abdo20050/BlackFingersTeam/models/3D Robot case.jpeg

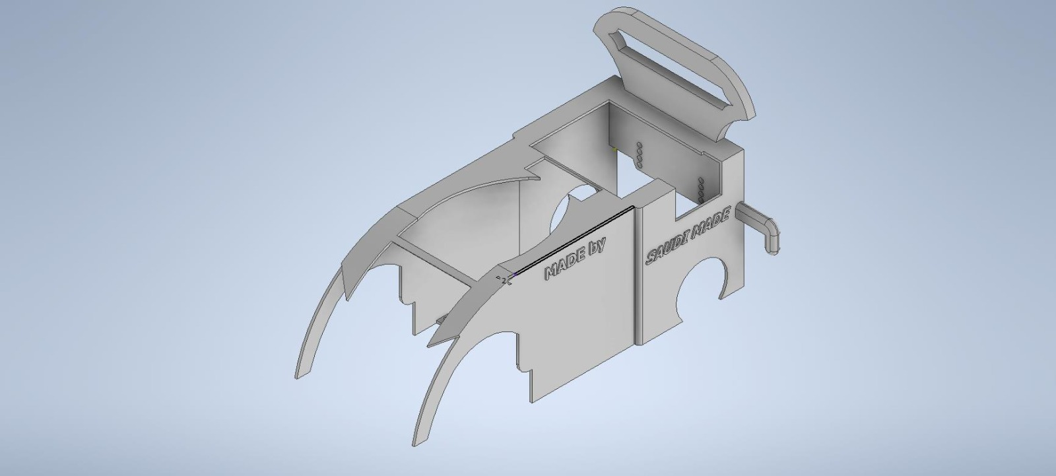
models/3D Robot case.jpeg
