abdo20050/BlackFingersTeam/models/3D vehicle structure main part.jpeg

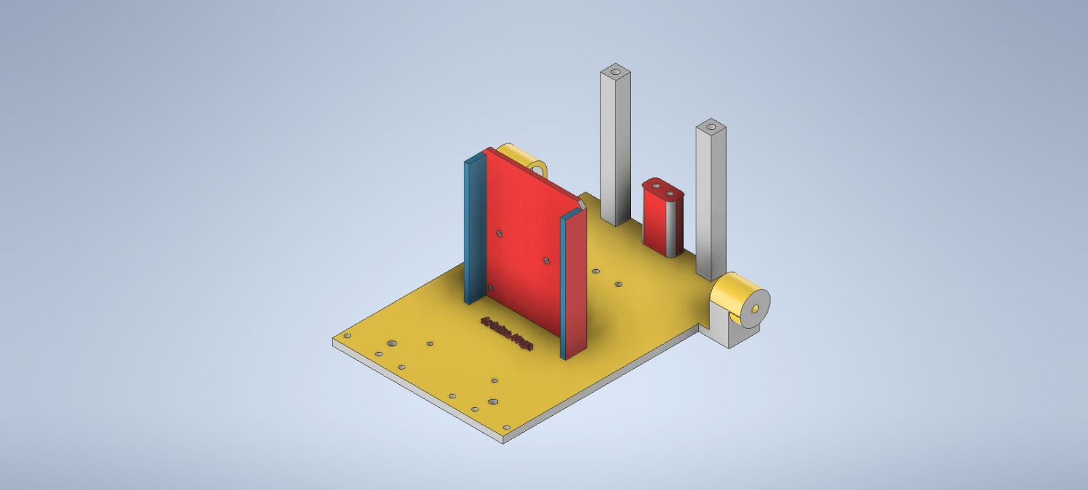
models/3D vehicle structure main part.jpeg
