abdo20050/BlackFingersTeam/models/acrylic pieces for wheels.jpg

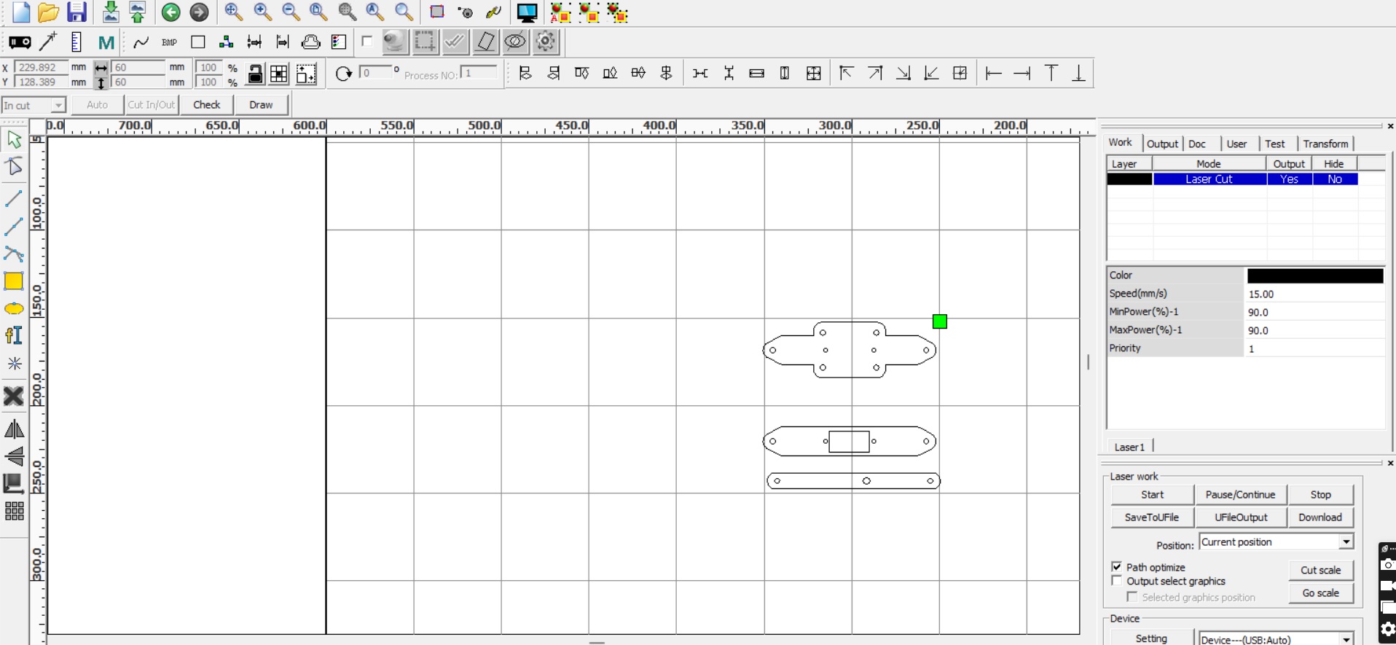
models/acrylic pieces for wheels.jpg
