abdo20050/BlackFingersTeam/models/ULTRASONIC BOX..jpg

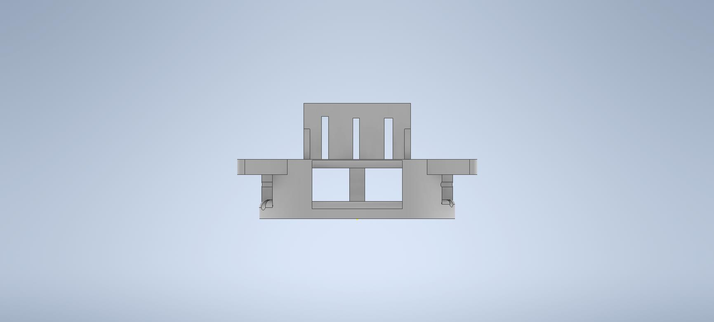
models/ULTRASONIC BOX..jpg
