abdo20050/BlackFingersTeam/schemes/circuit digram v2.jpeg

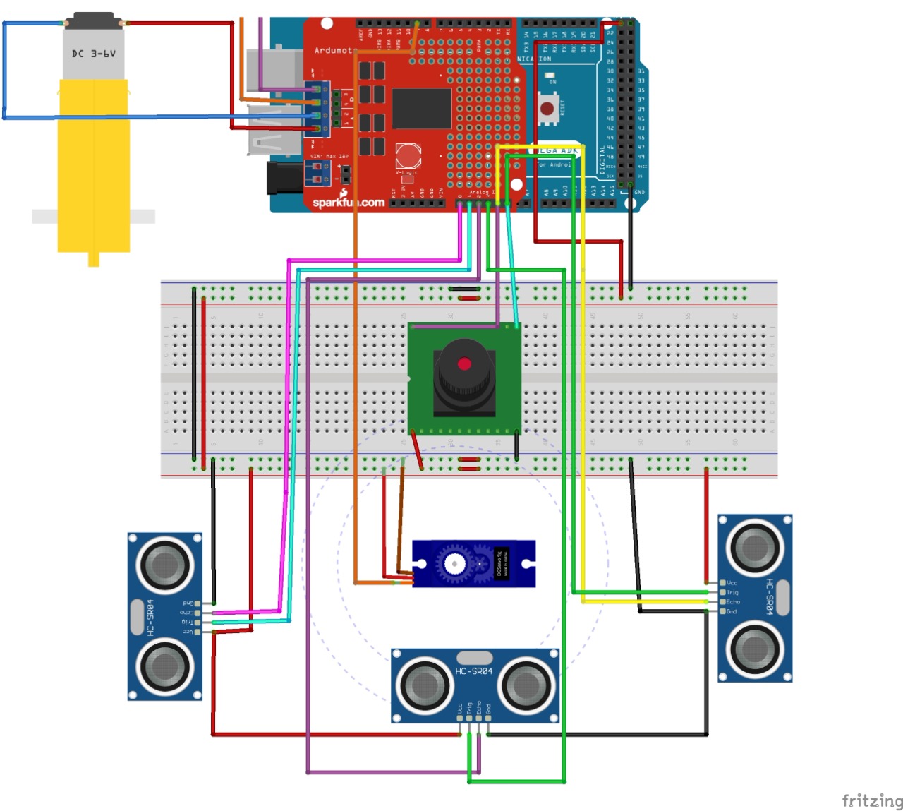
schemes/circuit digram v2.jpeg
