abdo20050/BlackFingersTeam/t - photos/FUNNY PHOTO.jpeg

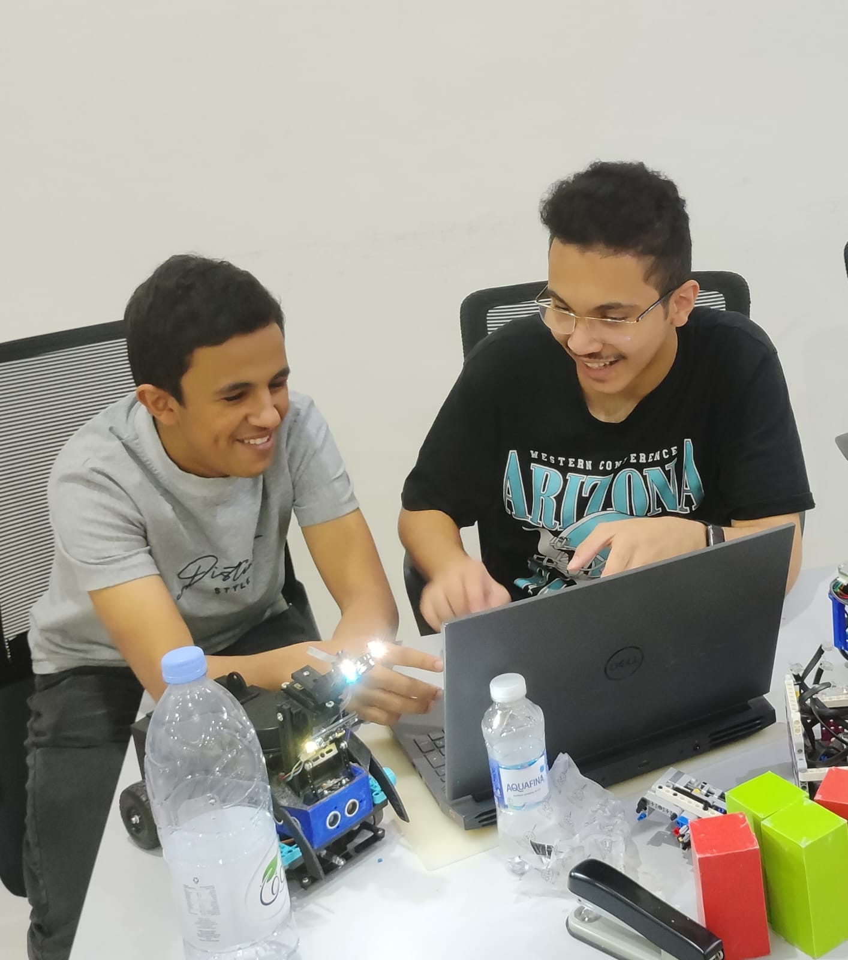
t - photos/FUNNY PHOTO.jpeg
