abdo20050/BlackFingersTeam/v- photos/DOWN SIDE.jpeg

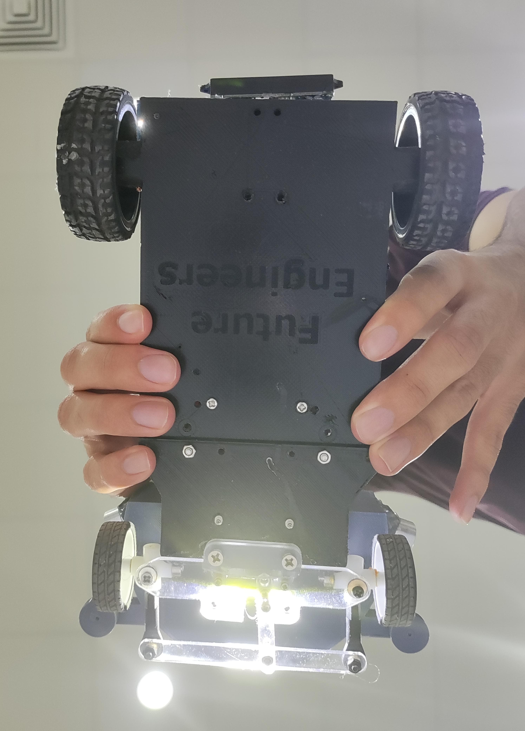
v- photos/DOWN SIDE.jpeg
