abdo20050/BlackFingersTeam/v- photos/FRONT SIDE.jpeg

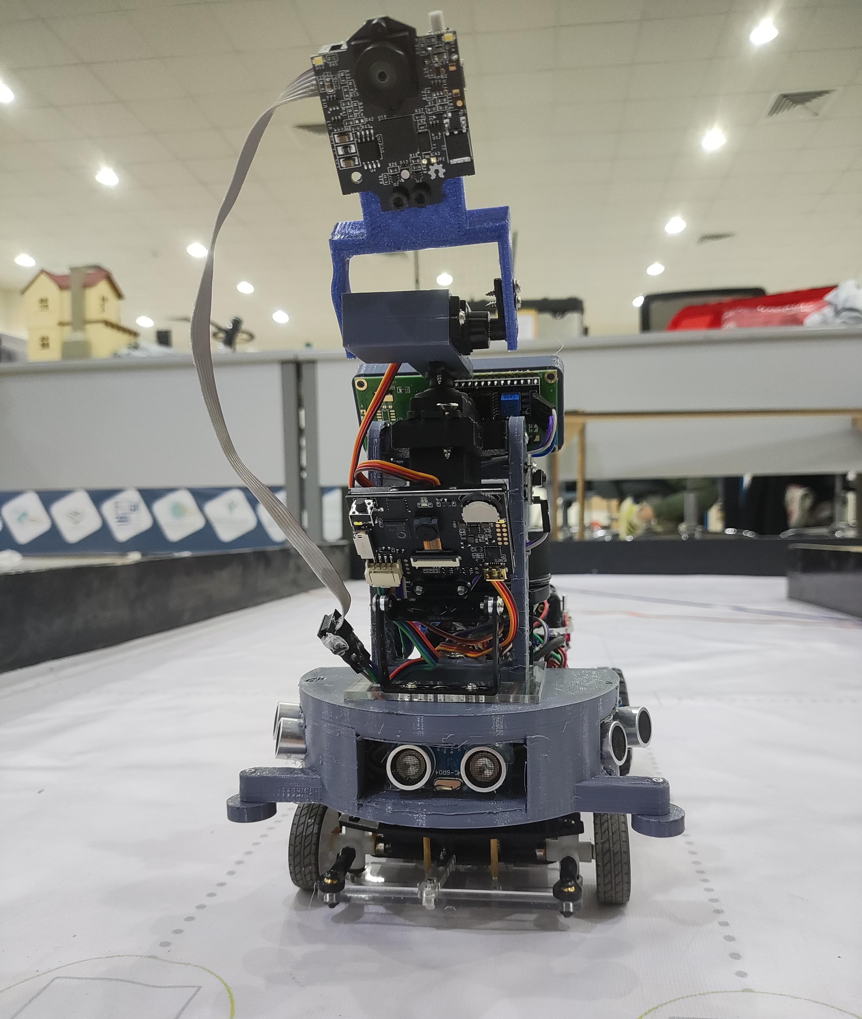
v- photos/FRONT SIDE.jpeg
