abdo20050/BlackFingersTeam/v- photos/LEFT SIDE.jpeg

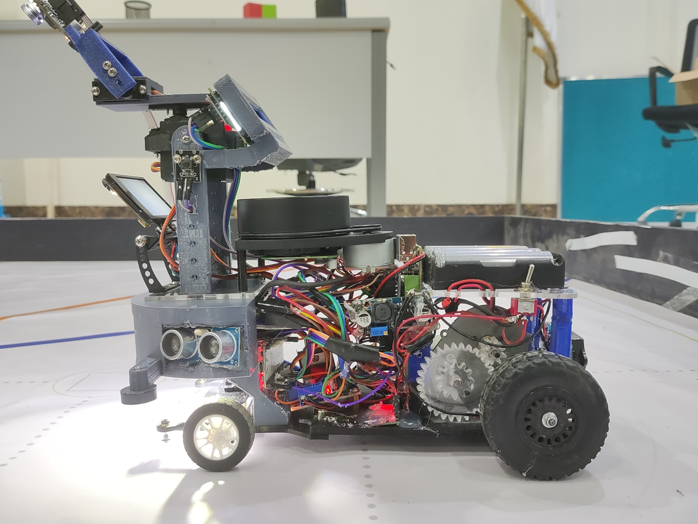
v- photos/LEFT SIDE.jpeg
