abdo20050/BlackFingersTeam/v- photos/RIGHT SIDE.jpeg

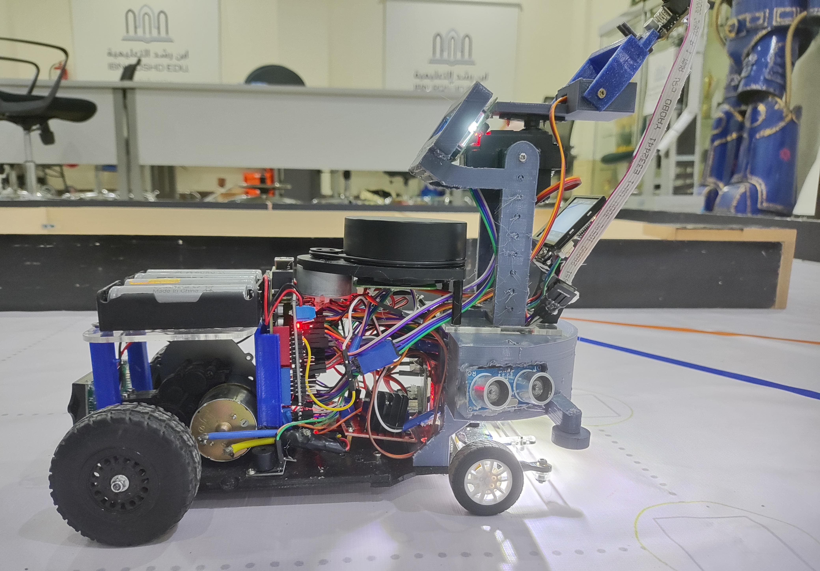
v- photos/RIGHT SIDE.jpeg
